ElectronicCats/badge-recon-2025/firmware/display_assets.h

#pragma once

// 'recon_logo', 128x32px
const unsigned char epd_bitmap_recon_logo[] PROGMEM = {
    0x00, 0x00, 0x00, 0x00, 0x00, 0x00, 0x00, 0x00, 0x00, 0x00, 0x00, 0x00,
    0x00, 0x00, 0x00, 0x00, 0x00, 0x00, 0x00, 0x00, 0x00, 0x00, 0x00, 0x00,
    0x00, 0x00, 0x00, 0x00, 0x00, 0x00, 0x00, 0x00, 0x00, 0x00, 0x00, 0x00,
    0x00, 0x00, 0x00, 0x00, 0x00, 0x00, 0x00, 0x00, 0x00, 0x00, 0x00, 0x00,
    0x00, 0x00, 0x00, 0x00, 0x00, 0x00, 0x00, 0x00, 0x00, 0x00, 0x00, 0x00,
    0x00, 0x00, 0x00, 0x00, 0x3f, 0xff, 0xf8, 0x07, 0xff, 0xff, 0x83, 0xff,
    0xff, 0xc1, 0xff, 0xff, 0x03, 0x80, 0x00, 0xe0, 0x3f, 0xff, 0xfc, 0x0f,
    0xff, 0xff, 0x87, 0xff, 0xff, 0xc3, 0xff, 0xff, 0x87, 0xc0, 0x00, 0xf8,
    0x3f, 0xff, 0xfe, 0x0f, 0xff, 0xff, 0x8f, 0xff, 0xff, 0x87, 0x00, 0x01,
    0xc7, 0xe0, 0x00, 0xfc, 0x38, 0x00, 0x07, 0x1e, 0x00, 0x00, 0x0e, 0x00,
    0x00, 0x0e, 0x00, 0x00, 0x03, 0x70, 0x00, 0xe0, 0x38, 0x00, 0x07, 0x1c,
    0x00, 0x00, 0x1c, 0x00, 0x00, 0x0e, 0x00, 0x00, 0xc7, 0x3c, 0x00, 0xe0,
    0x38, 0x00, 0x03, 0x1c, 0x00, 0x00, 0x1c, 0x00, 0x00, 0x0e, 0x00, 0x00,
    0xc7, 0x1f, 0x07, 0xe0, 0x38, 0x00, 0x03, 0x1f, 0xff, 0xff, 0x9c, 0x00,
    0x00, 0x0f, 0xfe, 0x00, 0xc7, 0x0f, 0x00, 0xe0, 0x38, 0x00, 0x07, 0x1f,
    0xff, 0xff, 0x9c, 0x00, 0x00, 0x0e, 0x00, 0x00, 0xc7, 0x03, 0xc0, 0xe0,
    0x3f, 0xff, 0xfe, 0x1f, 0xff, 0xff, 0x9c, 0x00, 0x00, 0x0e, 0x00, 0x00,
    0xc7, 0x01, 0xe0, 0xf8, 0x3f, 0xff, 0xfc, 0x1c, 0x00, 0x00, 0x1c, 0x00,
    0x00, 0x0e, 0x00, 0x00, 0xc6, 0x00, 0x70, 0xe0, 0x3f, 0xff, 0xf8, 0x1c,
    0x00, 0x00, 0x1c, 0x00, 0x00, 0x0e, 0x00, 0x00, 0xc6, 0x00, 0x38, 0xe0,
    0x3c, 0x00, 0x3c, 0x1e, 0x00, 0x00, 0x1c, 0x00, 0x00, 0x0e, 0x00, 0x0e,
    0xc7, 0x00, 0x1e, 0xe0, 0x3c, 0x00, 0x1e, 0x1f, 0xff, 0xff, 0x0e, 0x00,
    0x00, 0x07, 0x00, 0x03, 0xf7, 0x00, 0x0f, 0xe0, 0x3c, 0x00, 0x0f, 0x0f,
    0xff, 0xff, 0x8f, 0xff, 0xff, 0xc3, 0xff, 0xff, 0x87, 0x00, 0x01, 0xe0,
    0x3c, 0x00, 0x07, 0x8f, 0xff, 0xff, 0x87, 0xff, 0xff, 0xc1, 0xff, 0xff,
    0x07, 0x00, 0x01, 0xc0, 0x18, 0x00, 0x03, 0xc3, 0xff, 0xff, 0x81, 0xff,
    0xff, 0xc0, 0x7f, 0xfe, 0x02, 0x00, 0x00, 0x80, 0x00, 0x00, 0x00, 0x00,
    0x00, 0x00, 0x00, 0x00, 0x00, 0x00, 0x00, 0x00, 0x00, 0x00, 0x00, 0x00,
    0x00, 0x00, 0x00, 0x00, 0x00, 0x00, 0x00, 0x00, 0x00, 0x00, 0x00, 0x00,
    0x00, 0x00, 0x00, 0x00, 0x00, 0x00, 0x00, 0x00, 0x00, 0x00, 0x00, 0x00,
    0x00, 0x00, 0x00, 0x00, 0x00, 0x00, 0x00, 0x00, 0x00, 0x00, 0x00, 0x00,
    0x00, 0x00, 0x00, 0x00, 0x00, 0x00, 0x00, 0x00, 0x00, 0x00, 0x00, 0x00,
    0x00, 0x00, 0x00, 0x00, 0x00, 0x00, 0x00, 0x00, 0x00, 0x00, 0x00, 0xc7,
    0x18, 0xe0, 0x00, 0x00, 0x00, 0x00, 0x00, 0x00, 0x00, 0x00, 0x00, 0x00,
    0x00, 0x00, 0x01, 0x2d, 0xa5, 0x00, 0x00, 0x00, 0x00, 0x00, 0x00, 0x00,
    0x00, 0x00, 0x00, 0x00, 0x00, 0x00, 0x00, 0x28, 0x85, 0x00, 0x00, 0x00,
    0x00, 0x00, 0x00, 0x00, 0x00, 0x00, 0x00, 0x00, 0x00, 0x00, 0x00, 0x28,
    0x84, 0xc0, 0x00, 0x00, 0x00, 0x00, 0x00, 0x00, 0x00, 0x00, 0x00, 0x00,
    0x00, 0x00, 0x00, 0x48, 0x88, 0x20, 0x00, 0x00, 0x00, 0x00, 0x00, 0x00,
    0x00, 0x00, 0x00, 0x00, 0x00, 0x00, 0x00, 0x8d, 0x90, 0x20, 0x00, 0x00,
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
