ElectronicCats/badge-recon-2025/firmware/magspoof.ino

/************************************************************
  MagSpoof version for Bomber Cat
  by Salvador Mendoza (salmg.net)
  Electronic Cats (https://electroniccats.com/)

  This example demonstrates how to use Bomber Cat by Electronic Cats
  https://github.com/ElectronicCats/BomberCat

  Development environment specifics:
  IDE: Arduino 1.8.9
  Hardware Platform:
  Bomber Cat
  - RP2040

  Electronic Cats invests time and resources providing this open source code,
  please support Electronic Cats and open-source hardware by purchasing
  products from Electronic Cats!

  This code is beerware; if you see me (or any other Electronic Cats
  member) at the local, and you've found our code helpful,
  please buy us a round!
  Distributed as-is; no warranty is given.
*/
void blink(int pin, int msdelay, int times) {
  for (int i = 0; i < times; i++) {
    // digitalWrite(pin, HIGH);
    delay(msdelay);
    // digitalWrite(pin, LOW);
    delay(msdelay);
  }
}

// send a single bit out
void playBit(int sendBit) {
  dir ^= 1;
  digitalWrite(PIN_A, dir);
  digitalWrite(PIN_B, !dir);
  delayMicroseconds(CLOCK_US);

  if (sendBit) {
    dir ^= 1;
    digitalWrite(PIN_A, dir);
    digitalWrite(PIN_B, !dir);
  }
  delayMicroseconds(CLOCK_US);
}

// when reversing
void reverseTrack(int track) {
  int i = 0;
  track--;  // index 0
  dir = 0;

  while (revTrack[i++] != '\0')
    ;
  i--;
  while (i--)
    for (int j = bitlen[track] - 1; j >= 0; j--)
      playBit((revTrack[i] >> j) & 1);
}

// plays out a full track, calculating CRCs and LRC
void playTrack(int track) {
  int tmp, crc, lrc = 0;
  dir = 0;
  track--;  // index 0
  // enable H-bridge and LED
  // digitalWrite(ENABLE_PIN, HIGH);

  // First put out a bunch of leading zeros.
  for (int i = 0; i < 25; i++)
    playBit(0);

  for (int i = 0; tracks[track][i] != '\0'; i++) {
    crc = 1;
    tmp = tracks[track][i] - sublen[track];

    for (int j = 0; j < bitlen[track] - 1; j++) {
      crc ^= tmp & 1;
      lrc ^= (tmp & 1) << j;
      playBit(tmp & 1);
      tmp >>= 1;
    }
    playBit(crc);
  }

  // finish calculating and send last "byte" (LRC)
  tmp = lrc;
  crc = 1;
  for (int j = 0; j < bitlen[track] - 1; j++) {
    crc ^= tmp & 1;
    playBit(tmp & 1);
    tmp >>= 1;
  }
  playBit(crc);

  // if track 1, play 2nd track in reverse (like swiping back?)
  if (track == 0) {
    // if track 1, also play track 2 in reverse
    // zeros in between
    for (int i = 0; i < BETWEEN_ZERO; i++)
      playBit(0);

    // send second track in reverse
    reverseTrack(2);
  }

  // finish with 0's
  for (int i = 0; i < 5 * 5; i++)
    playBit(0);

  digitalWrite(PIN_A, LOW);
  digitalWrite(PIN_B, LOW);
}

// stores track for reverse usage later
void storeRevTrack(int track) {
  int i, tmp, crc, lrc = 0;
  track--;  // index 0
  dir = 0;

  for (i = 0; tracks[track][i] != '\0'; i++) {
    crc = 1;
    tmp = tracks[track][i] - sublen[track];

    for (int j = 0; j < bitlen[track] - 1; j++) {
      crc ^= tmp & 1;
      lrc ^= (tmp & 1) << j;
      tmp & 1 ? (revTrack[i] |= 1 << j) : (revTrack[i] &= ~(1 << j));
      tmp >>= 1;
    }
    crc ? (revTrack[i] |= 1 << 4) : (revTrack[i] &= ~(1 << 4));
  }

  // finish calculating and send last "byte" (LRC)
  tmp = lrc;
  crc = 1;
  for (int j = 0; j < bitlen[track] - 1; j++) {
    crc ^= tmp & 1;
    tmp & 1 ? (revTrack[i] |= 1 << j) : (revTrack[i] &= ~(1 << j));
    tmp >>= 1;
  }
  crc ? (revTrack[i] |= 1 << 4) : (revTrack[i] &= ~(1 << 4));

  i++;
  revTrack[i] = '\0';
}

void runMagspoof() {
  Adafruit_SSD1306* display = displayController.getDisplay();
  display->clearDisplay();
  display->setTextColor(SSD1306_WHITE);
  display->setCursor(0, 0);
  display->println(F("Emulating Magstripe"));
  display->println(F("Swipe card to read"));
  display->display();

  Serial.println("Activating MagSpoof...");
  Serial.print("Track 1: ");
  Serial.println(tracks[0]);
  Serial.print("Track 2: ");
  Serial.println(tracks[1]);

  playTrack(1 + (curTrack++ % 2));
  blink(L1, 150, 3);
  delay(400);

  display->clearDisplay();
  display->setTextColor(SSD1306_WHITE);
  display->setCursor(0, 0);
  display->println(F("Emulation complete"));
  display->println(F("Press BACK button"));
  display->display();

  // Wait for back button press
  while (!inputController.isBackPressed()) {
    inputController.update();
    delay(10);
  }
}

void setupTracks(String newTrack1, String newTrack2) {
  String track1 = "%B123456781234567^Mitnick/Kevin^YYMMSSSDDDDDDDDDDDDDDDDDDDDDDDDD?";
  String track2 = ";123456781234567=112220100000000000000?";

  if (newTrack1.length() > 0) {
    track1 = newTrack1;
  }

  if (newTrack2.length() > 0) {
    track2 = newTrack2;
  }

  // Copy the tracks into the char arrays using strcpy
  strcpy(tracks[0], track1.c_str());
  strcpy(tracks[1], track2.c_str());
}

void setupMagspoof() {
  pinMode(PIN_A, OUTPUT);
  pinMode(PIN_B, OUTPUT);
  // pinMode(L1, OUTPUT);

  setupTracks();

  // blink to show we started up
  blink(L1, 200, 2);
}
